LordRaptor/VoltmeterClock/images/Buttons.jpg

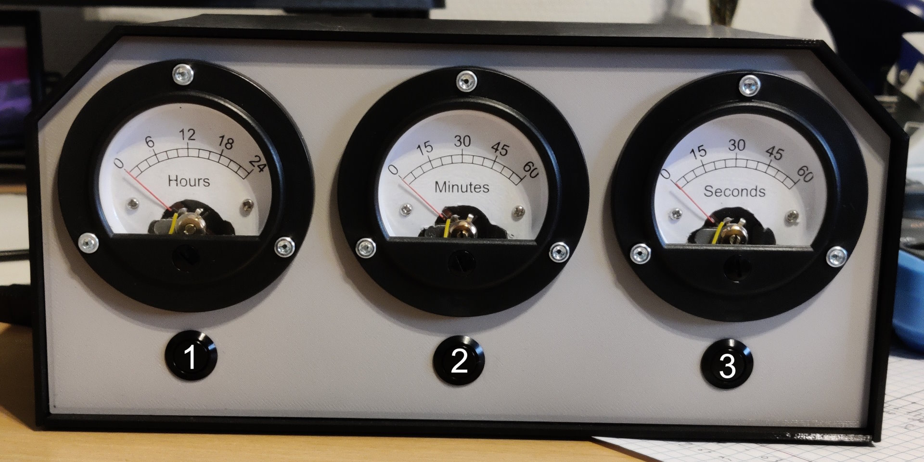
images/Buttons.jpg
